madskjeldgaard/mico/assets/mico-3d-2.jpg

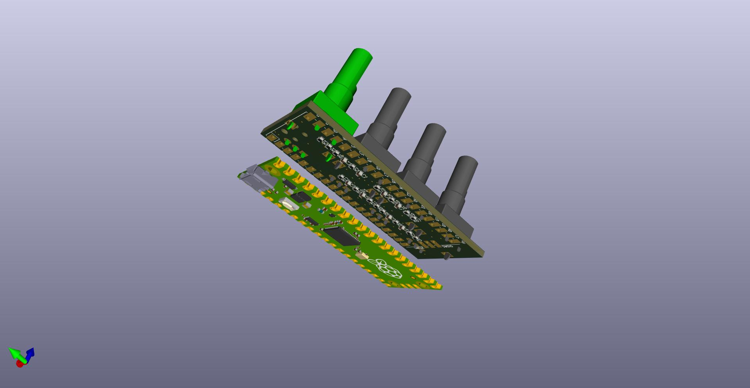
assets/mico-3d-2.jpg
