madskjeldgaard/mico/assets/mico-3d.jpg

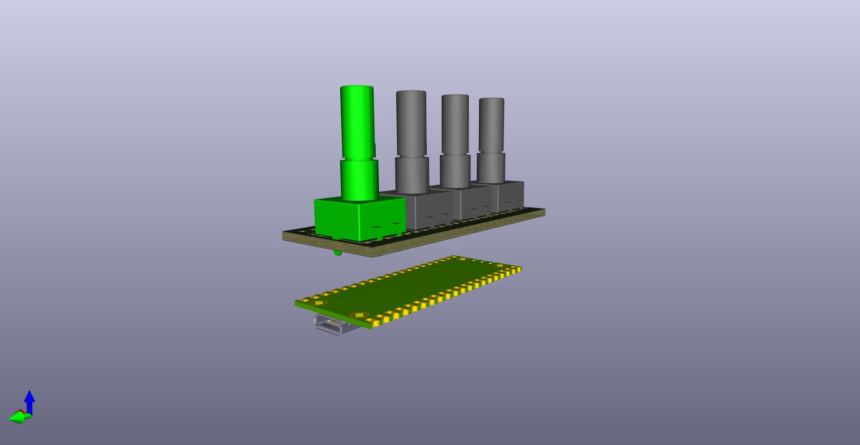
assets/mico-3d.jpg
