madskjeldgaard/mico/micopcb1.png

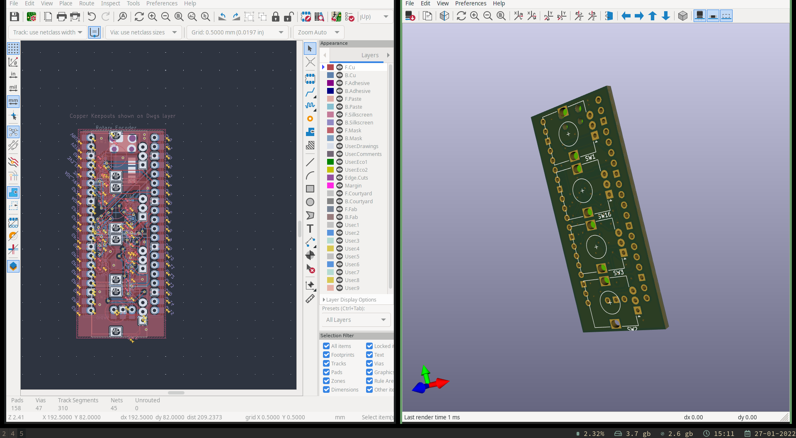
micopcb1.png
