madskjeldgaard/mico/micopcb2.png

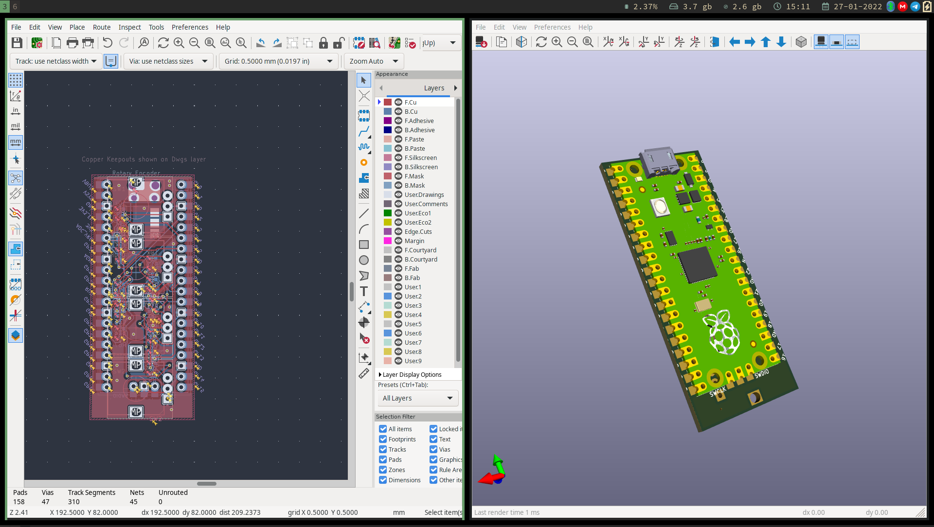
micopcb2.png
